fabriziofiorucci/Tapeosaurus/CAD/stl/P.stl

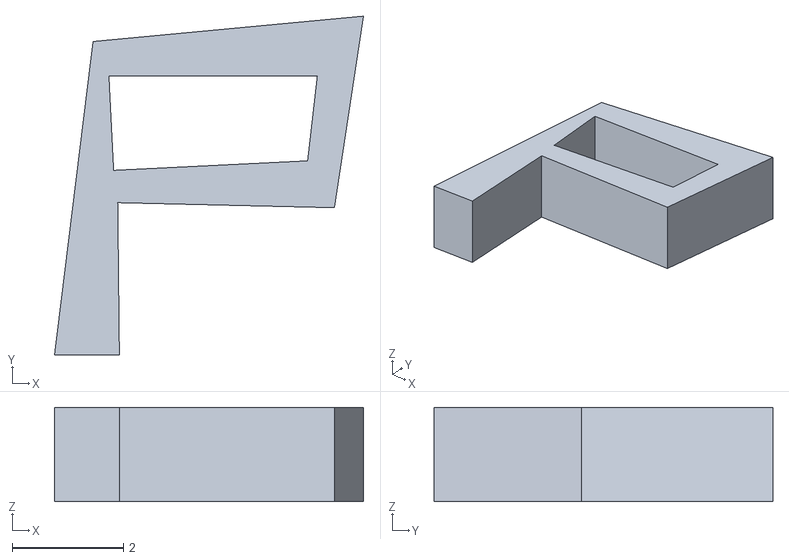
[picture p26: CAD file, 2026-05-26]
CAD/stl/P.stl
5.57 x 6.10 x 1.70
