fabriziofiorucci/Tapeosaurus/CAD/stl/E.stl

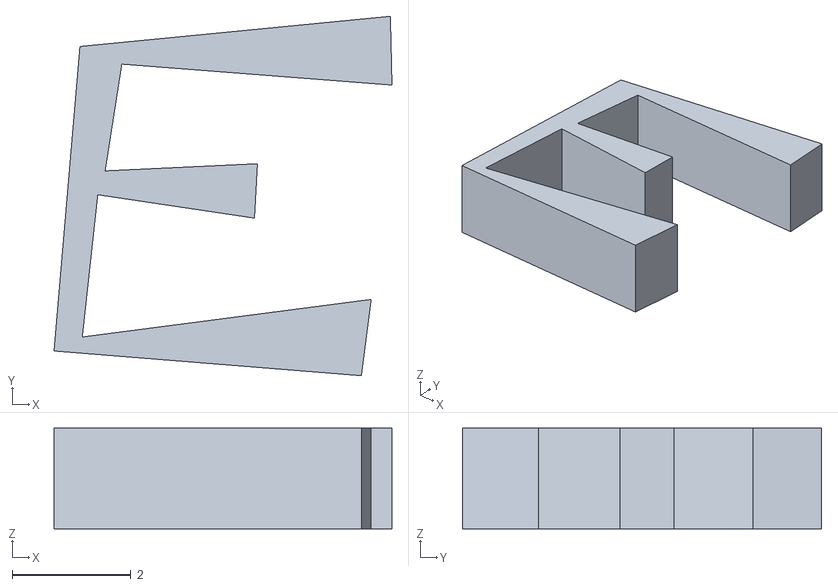
[picture p27: CAD file, 2026-05-26]
CAD/stl/E.stl
5.70 x 6.06 x 1.70
