fabriziofiorucci/Tapeosaurus/CAD/stl/On 1.stl

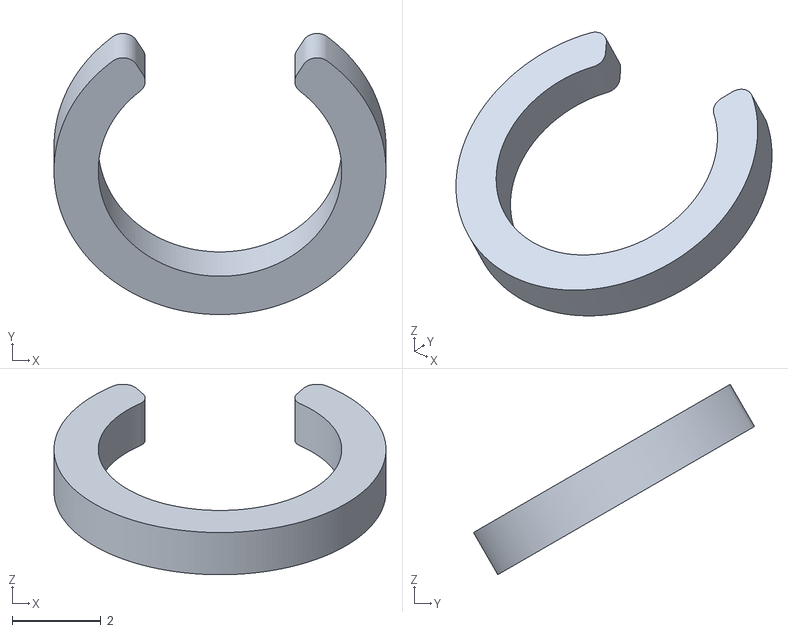
[picture p28: CAD file, 2026-05-26]
CAD/stl/On 1.stl
7.50 x 6.35 x 4.30
