fabriziofiorucci/Tapeosaurus/CAD/stl/Play.stl

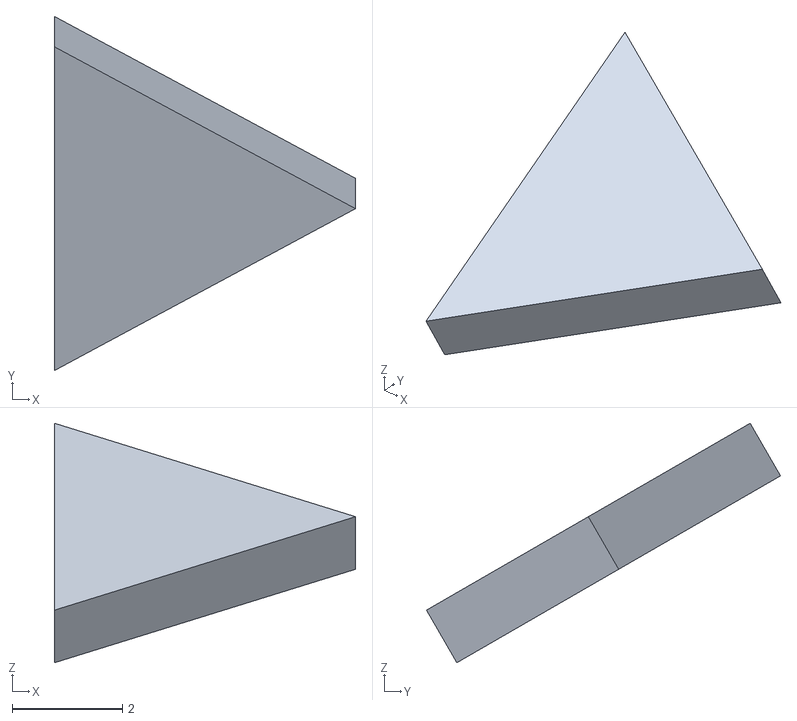
[picture p29: CAD file, 2026-05-26]
CAD/stl/Play.stl
5.45 x 6.41 x 4.34
