fabriziofiorucci/Tapeosaurus/CAD/stl/Tapeosaurus - Lid.stl

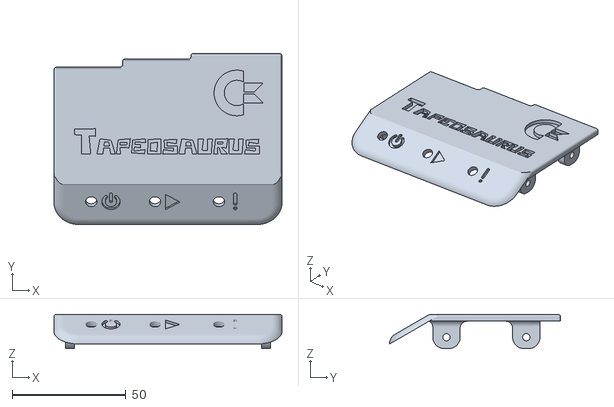
[picture p30: CAD file, 2026-05-24]
CAD/stl/Tapeosaurus - Lid.stl
100.0 x 75.0 x 15.0
